j-w-e/wysteria/images/2.jpg

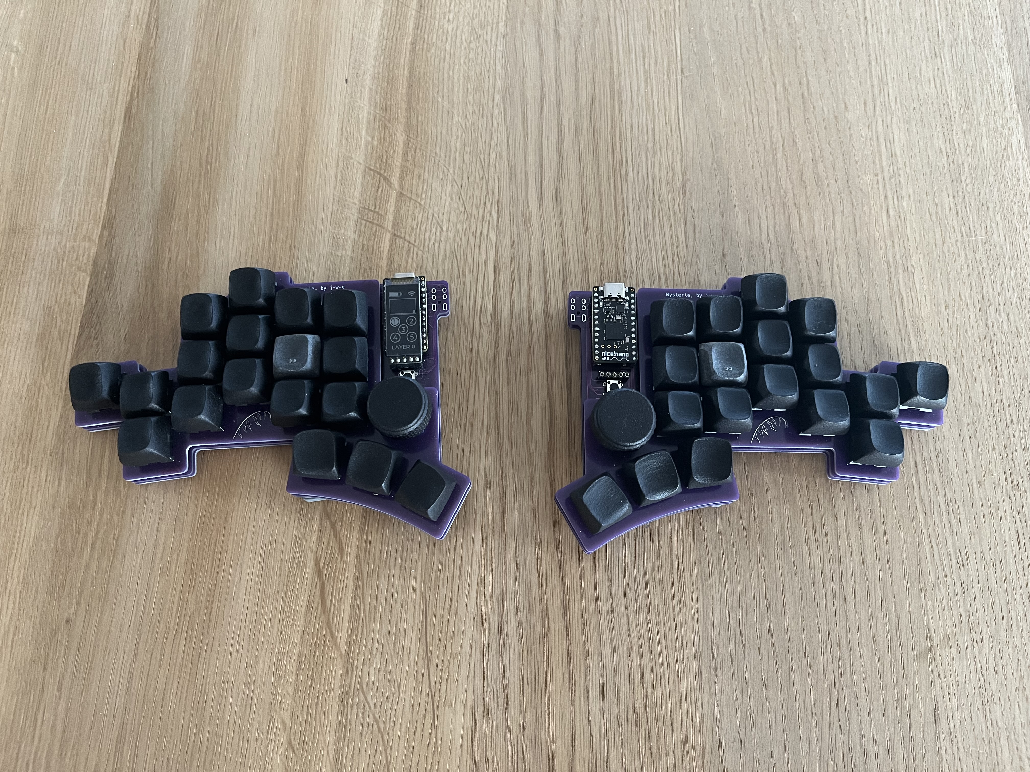
images/2.jpg
