j-w-e/wysteria/images/3.jpg

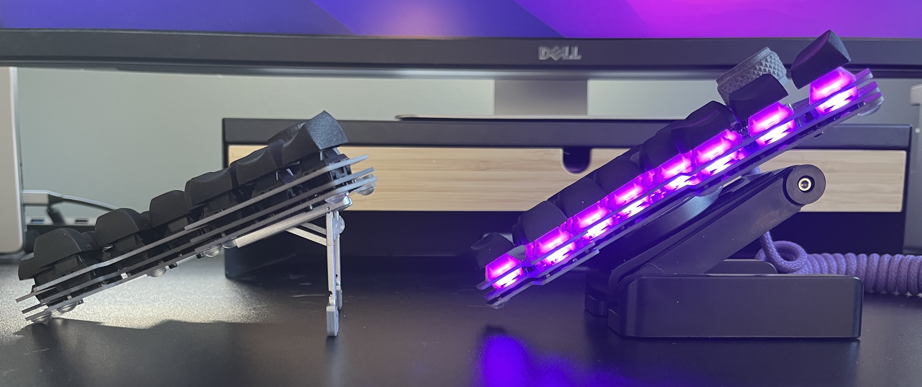
images/3.jpg
