j-w-e/wysteria/ergogen/output/outlines/_controller1.dxf

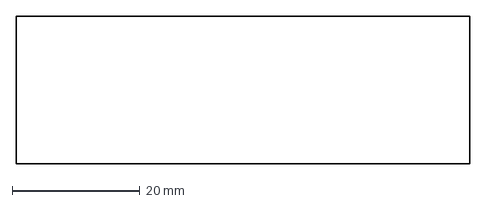
[picture p18: CAD file, 2024-03-10]
ergogen/output/outlines/_controller1.dxf
71.0 x 23.0 mm
