j-w-e/wysteria/ergogen/output/outlines/_extension_for_inner.dxf

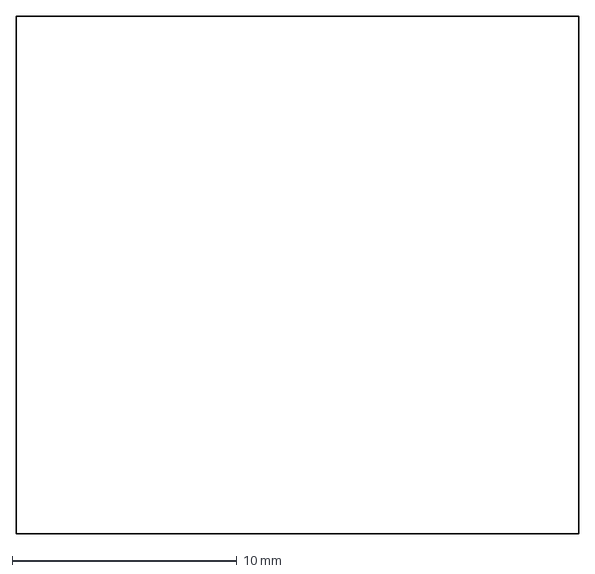
[picture p19: CAD file, 2024-03-10]
ergogen/output/outlines/_extension_for_inner.dxf
25.0 x 23.0 mm
