j-w-e/wysteria/ergogen/output/outlines/_screws.dxf

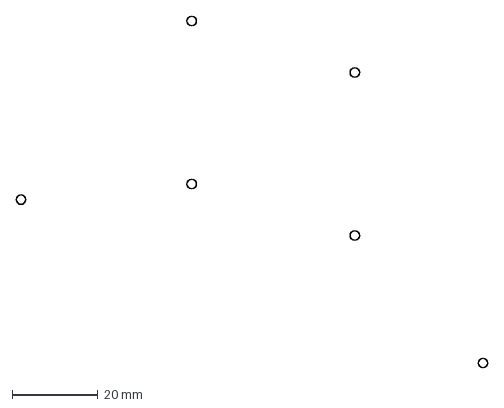
[picture p20: CAD file, 2024-03-10]
ergogen/output/outlines/_screws.dxf
109.8 x 81.9 mm
