j-w-e/wysteria/ergogen/output/outlines/_screws.yaml

models:
    export:
        models:
            a:
                models:
                    a:
                        models:
                            a:
                                models:
                                    a:
                                        models:
                                            a:
                                                models:
                                                    a:
                                                        models: {}
                                                        origin:
                                                            - 0
                                                            - 0
                                                    b:
                                                        paths:
                                                            circle:
                                                                type: circle
                                                                origin:
                                                                    - 106.3447993
                                                                    - -177.15557049999998
                                                                radius: 1.1
                                                        origin:
                                                            - 0
                                                            - 0
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
                            - 213.94348309999998
                            - -215.21713330000006
                        radius: 1.1
                origin:
                    - 0
                    - 0
        origin:
            - 0
            - 0
units: mm
origin:
    - 0
    - 0
